herbstmensch/BrewDuino/Kochen.ino

int kochzeit = 90;
int anzahlHopfengaben = 3;
int hopfengaben[10] = {0, 0, 0, 0, 0, 0, 0, 0, 0, 0};
int aktuelleHopfengabe = 1;
int alertedHopfengaben = 0;

State stateReachKochTemp = State(prepareReachKochTemp, reachKochTemp, prepareKochDauer);
State stateWaitKochDauer = State(waitKochDauer);
State stateAlertHopfengabe = State(alertHopfengabe);
FSM fsmKochProzess = FSM(stateReachKochTemp);

void enterKochzeit() {
  encoderValue = encoder->getValue();
  if (encoderValue != 0 || first) {
    first = false;
    kochzeit += encoderValue;
    if (kochzeit < 1)
      kochzeit = 1;

    clrScr(false, false);
    lcd.print("Kochzeit:", 0, 16);
    lcd.invertText(true);
    lcd.printNumI(int(kochzeit), 15, 24);
    lcd.invertText(false);
    lcd.print(" min", 29, 24);
  }

  if (buttonClicked()) {
    fsmKochen.immediateTransitionTo(stateEnterAnzahlHopfengaben);
  }
}

void enterAnzahlHopfengaben() {
  encoderValue = encoder->getValue();
  if (encoderValue != 0 || first) {
    first = false;
    anzahlHopfengaben += encoderValue;
    if (anzahlHopfengaben < 0)
      anzahlHopfengaben = 0;
    if (anzahlHopfengaben > 10)
      anzahlHopfengaben = 10;

    clrScr(false, false);
    lcd.print("Anz. Hopfeng.", 0, 16);
    lcd.invertText(true);
    lcd.printNumI(int(anzahlHopfengaben), 15, 24);
    lcd.invertText(false);
  }

  if (buttonClicked()) {
    first = true;
    if (anzahlHopfengaben > 0) {
      aktuelleHopfengabe = 0;
      first = true;
      hopfengaben[aktuelleHopfengabe] = 20 > kochzeit ? kochzeit : 20;
      fsmKochen.immediateTransitionTo(stateDefineHopfengaben);
    }
    else {
      fsmKochen.immediateTransitionTo(stateDoKochen);
    }
  }
}

void defineHopfengaben() {
  encoderValue = encoder->getValue();
  if (encoderValue != 0 || first) {
    first = false;
    hopfengaben[aktuelleHopfengabe] += encoderValue;
    Serial.print(hopfengaben[aktuelleHopfengabe]);

    if (aktuelleHopfengabe > 0) {
      //Hopfengabe muss nach der vorangegangenen liegen
      if (hopfengaben[aktuelleHopfengabe] <= hopfengaben[aktuelleHopfengabe - 1])
        hopfengaben[aktuelleHopfengabe] = hopfengaben[aktuelleHopfengabe - 1] + 1;
    }
    //Hopfenhabe darf nicht nach Kochende liegen
    if (hopfengaben[aktuelleHopfengabe] > kochzeit)
      hopfengaben[aktuelleHopfengabe] = kochzeit;

    clrScr(false, false);
    lcd.printNumI(int(aktuelleHopfengabe + 1), 8, 12);
    lcd.print(". Hopfeng.", 15 + (aktuelleHopfengabe > 9 ? 7 : 0), 12);
    lcd.print("Nach :", 15, 20);
    lcd.invertText(true);
    lcd.printNumI(int(hopfengaben[aktuelleHopfengabe]), 57, 20);
    lcd.invertText(false);
    lcd.print("Minuten", 15, 28);
  }

  if (buttonClicked()) {
    aktuelleHopfengabe += 1;
    if (aktuelleHopfengabe + 1 > anzahlHopfengaben) {
      fsmKochen.immediateTransitionTo(stateDoKochen);
    } else {
      hopfengaben[aktuelleHopfengabe] = hopfengaben[aktuelleHopfengabe - 1] + 1;
      first = true;
    }
  }
}

void enterDoKochen() {
  first = true;
  alertedHopfengaben = -1;
  fsmKochProzess.immediateTransitionTo(stateReachKochTemp);
}

void doKochen() {
  fsmKochProzess.update();
}

void prepareReachKochTemp() {
  first=true;
}
void reachKochTemp() {
  if (first) {
    first = false;
    clrScr(false, false);

    lcd.print("Warte auf", CENTER, 16);
    lcd.print("Kochtemp.", CENTER, 24);

    snprintf(lcdBuf, sizeof(lcdBuf), "%i~ C\0", sollTemp);
    lcd.print(lcdBuf, CENTER, 32);
  }

  if (temp >= sollTemp) {
    fsmKochProzess.immediateTransitionTo(stateWaitKochDauer);
  }
}

void prepareKochDauer() {
  lastRest = MAX_LONG;
  storedSystemMillis = millis();
  dauer = kochzeit * 60 * 1000L;
  alertedHopfengaben = 0;
}

void waitKochDauer() {
  long rest = dauer - (millis() - storedSystemMillis);

  //Anzeige nur ändern, wenn eine Sekunde vergangen ist.
  if (lastRest - rest >= 500) {
    lastRest = rest;
    int std = ((rest / 1000) / 60) / 60;
    int min = ((rest / 1000) / 60) % 60;
    int sec = (rest / 1000) % 60;

    clrScr(false, false);
    lcd.print("Kochen:", CENTER, 16);
    Serial.println(rest);
    if (std > 0) {
      snprintf(lcdBuf, sizeof(lcdBuf), (rest / 500) % 2 == 0 ? "noch %.2i:%.2i:%.2i\0" : "noch %.2i %.2i %.2i\0", std, min, sec);
    } else {
      snprintf(lcdBuf, sizeof(lcdBuf), (rest / 500) % 2 == 0 ? "%noch 02d:%02d\0" : "noch %02d %02d\0", min, sec);
    }
    lcd.print(lcdBuf, CENTER, 24);
  }
  
  //Hopfengabe?
  if (anzahlHopfengaben - 1 > alertedHopfengaben) {
    long hg = hopfengaben[alertedHopfengaben] * 60 * 1000L;
    long verstrichen = (millis() - storedSystemMillis);
    if (verstrichen > hg) {
      alertedHopfengaben += 1;
      first = true;
      fsmKochProzess.immediateTransitionTo(stateAlertHopfengabe);
    }
  }



  if (rest <= 0) {
    alarm();
    fsmMain.immediateTransitionTo(stateMenu);
  }
}

unsigned long hgMillis;

void alertHopfengabe() {
  if (first) {
    first=false;
    alarm();
    hgMillis = alertMillis;
    clrScr(false, false);

    snprintf(lcdBuf, sizeof(lcdBuf), "%i. Hopfeng.\0", (alertedHopfengaben));
    lcd.print(lcdBuf, CENTER, 16);

    snprintf(lcdBuf, sizeof(lcdBuf), "%i min. Kochz.\0", hopfengaben[alertedHopfengaben-1]);
    lcd.print(lcdBuf, CENTER, 24);
  }

  if (buttonClicked()) {
    cancelAlarm();
    fsmKochProzess.immediateTransitionTo(stateWaitKochDauer);
  }

  //Nach spät. 1 min. die Hopfengabe ausblenden
  if (millis() - hgMillis >= 60000) {
    fsmKochProzess.immediateTransitionTo(stateWaitKochDauer);
  }

}
